dashan914/detective-camera/demo/screen-frames/capturing-talking.png

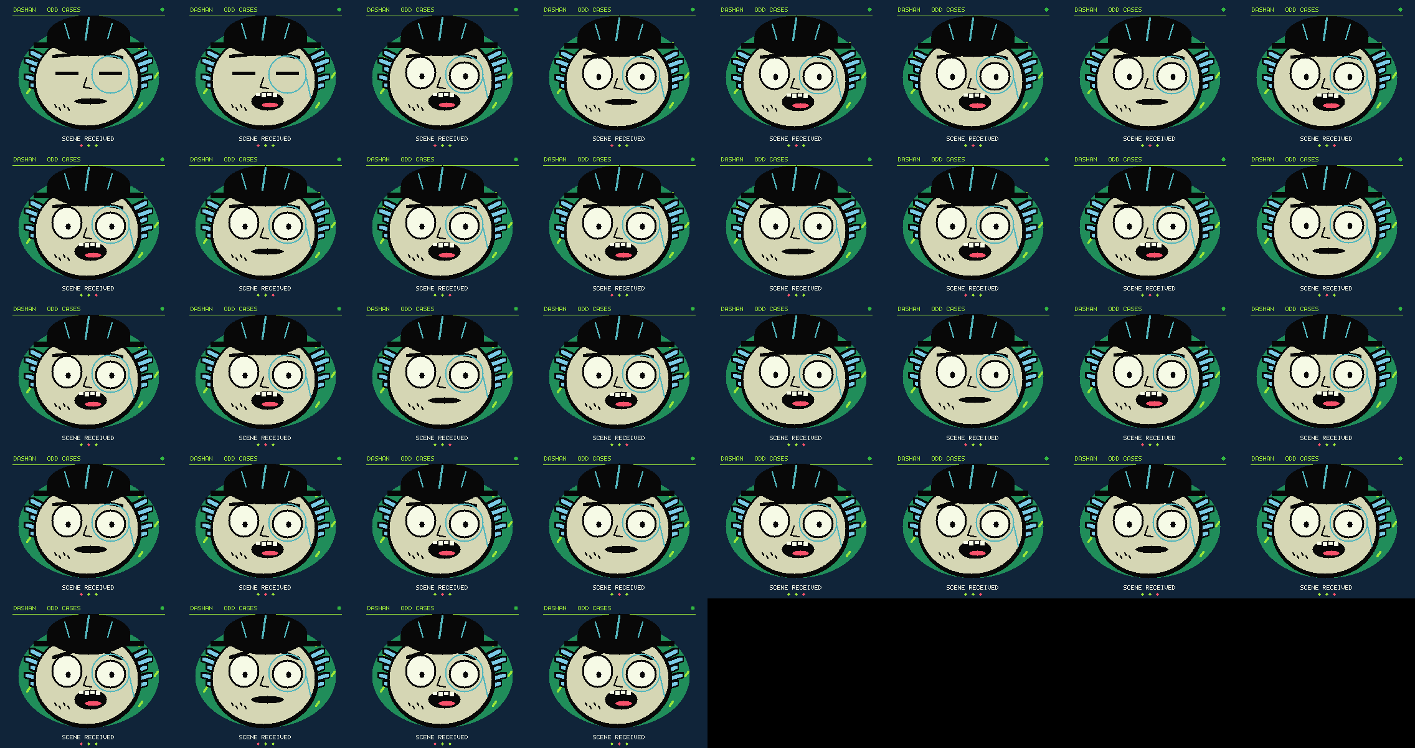
demo/screen-frames/capturing-talking.png
