dashan914/detective-camera/hardware/stl/11_DASHAN_rectangular_badge.stl

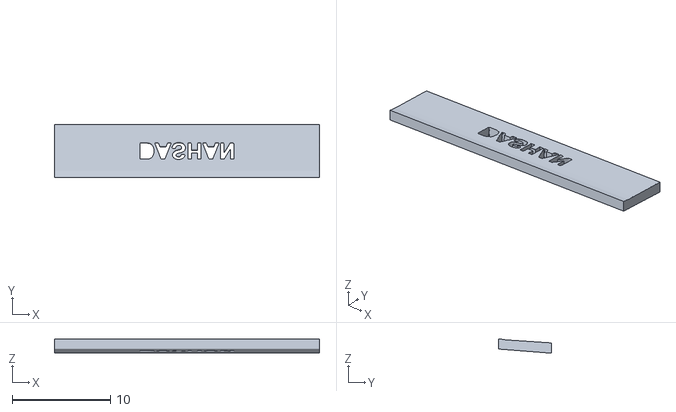
[picture p20: CAD file, 2026-10-03]
hardware/stl/11_DASHAN_rectangular_badge.stl
27.0 x 5.40 x 1.46
