dashan914/detective-camera/hardware/stl/33_LCD183_carrier.stl

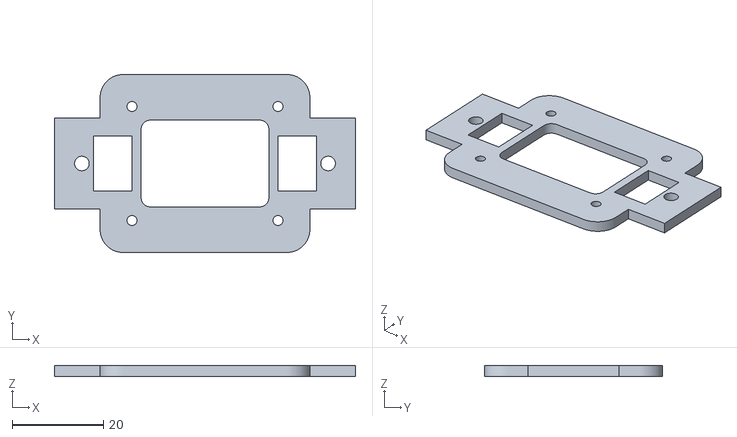
[picture p21: CAD file, 2026-10-03]
hardware/stl/33_LCD183_carrier.stl
66.0 x 39.0 x 2.40
