dashan914/detective-camera/hardware/stl/18_Paper_spindle.stl

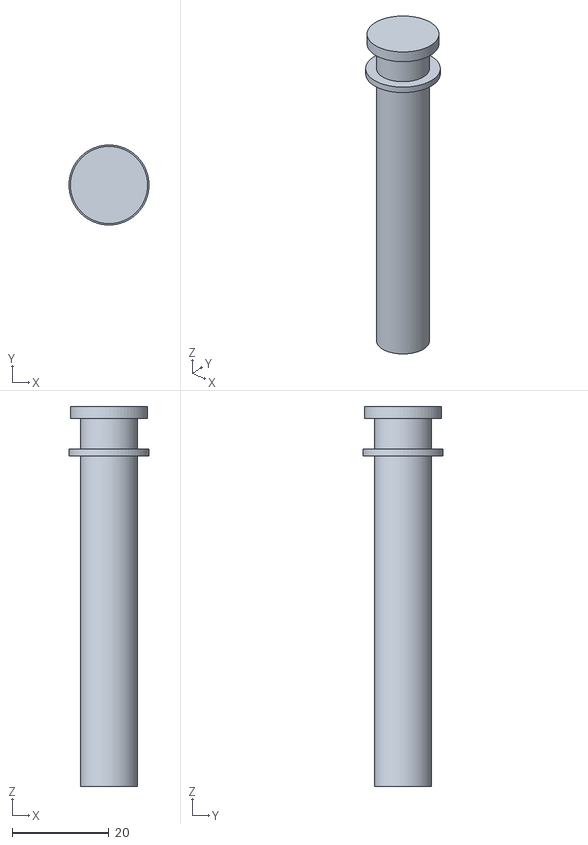
[picture p22: CAD file, 2026-10-03]
hardware/stl/18_Paper_spindle.stl
16.6 x 16.6 x 78.8
