dashan914/detective-camera/hardware/stl/03_Base_tray.stl

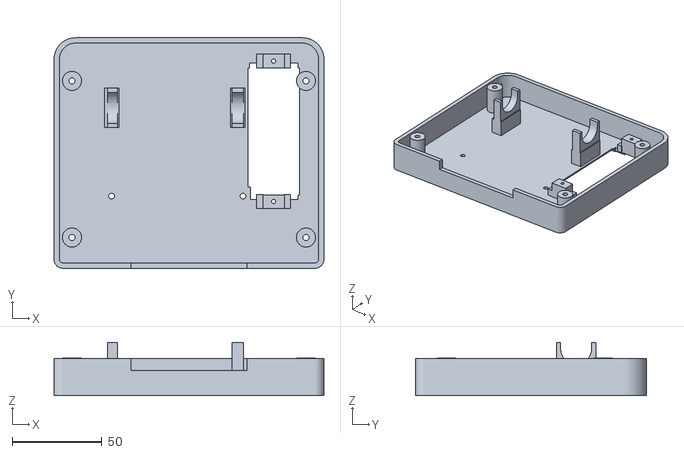
[picture p23: CAD file, 2026-10-03]
hardware/stl/03_Base_tray.stl
150.0 x 128.1 x 29.5
