dashan914/detective-camera/hardware/stl/31_Printer_left_integral.stl

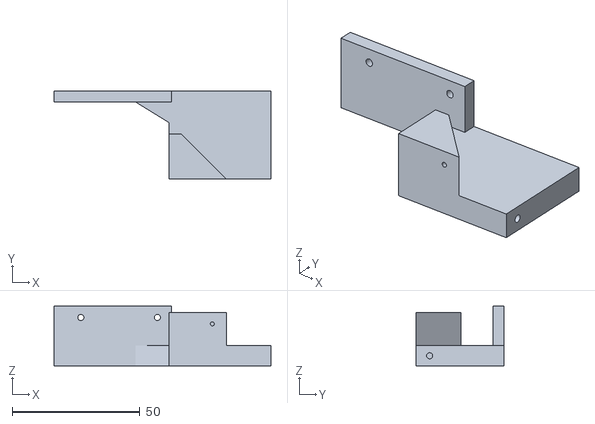
[picture p24: CAD file, 2026-10-03]
hardware/stl/31_Printer_left_integral.stl
85.0 x 34.6 x 23.5
