dashan914/detective-camera/hardware/stl/06_Rounded_shutter_cap.stl

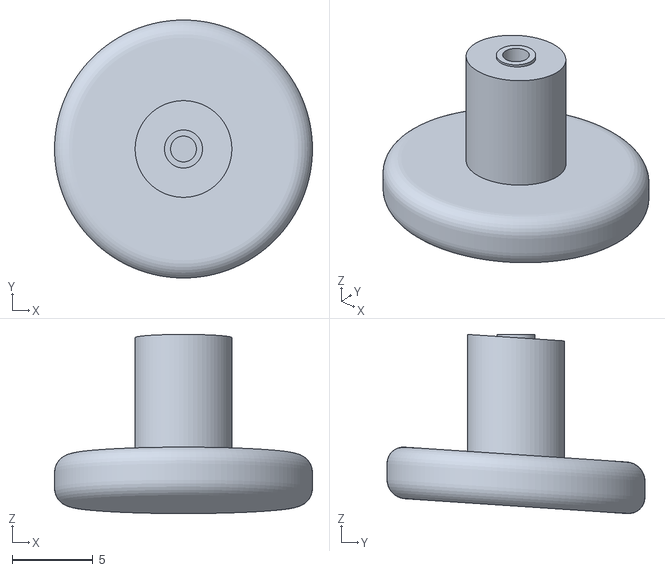
[picture p25: CAD file, 2026-10-03]
hardware/stl/06_Rounded_shutter_cap.stl
16.0 x 16.0 x 11.1
