dashan914/detective-camera/hardware/stl/25_Shutter_switch_holder.stl

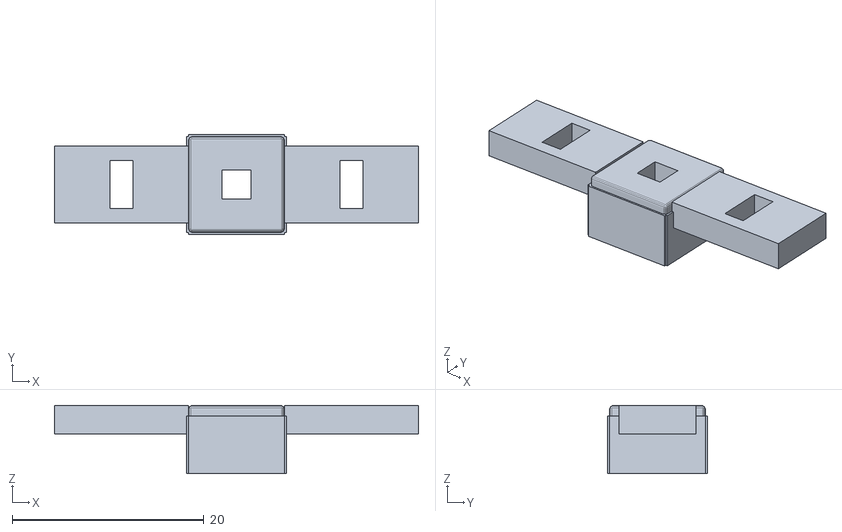
[picture p26: CAD file, 2026-10-03]
hardware/stl/25_Shutter_switch_holder.stl
38.0 x 10.4 x 7.10
